cadextcp/taito-rotary-stick/exports/rotary_stick/vorschau_schnitt.png

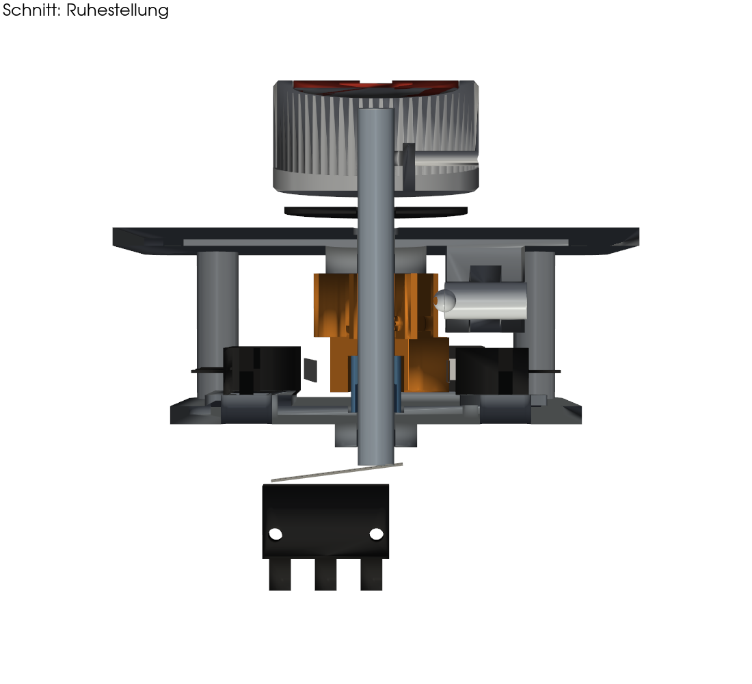
exports/rotary_stick/vorschau_schnitt.png
